Ottercast/OtterCastAmp/graphics/ottercast/enig.png

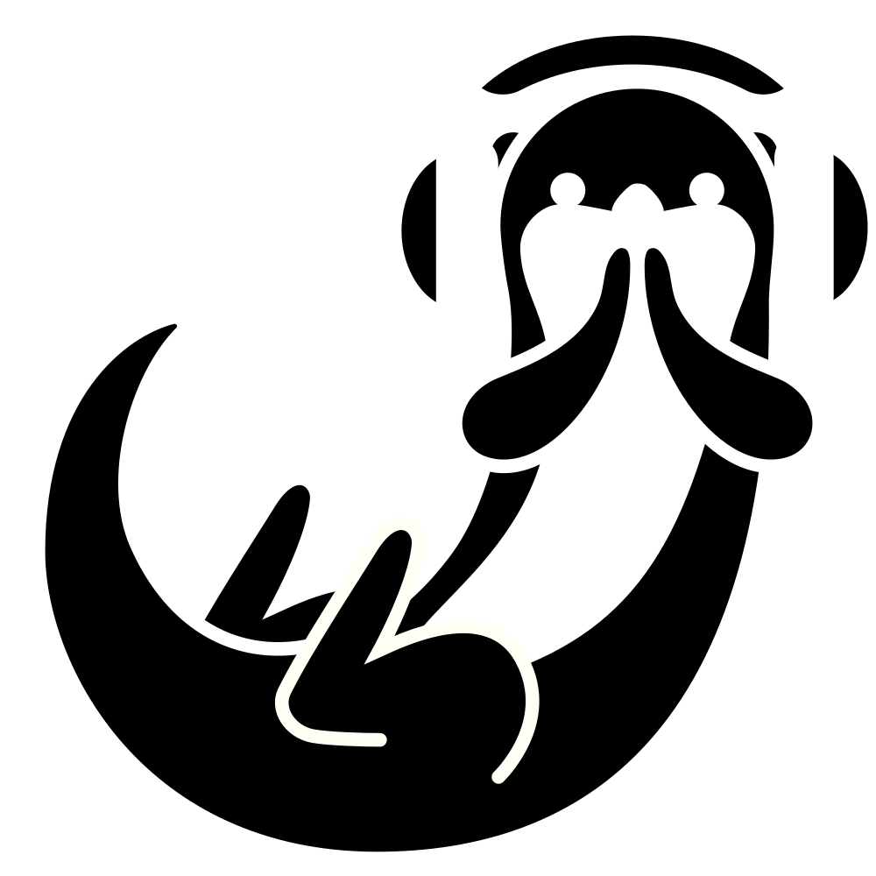
graphics/ottercast/enig.png
