Ottercast/OtterCastAmp/3D/u.Fl Antenna Connector - 523-A-1JB.STEP

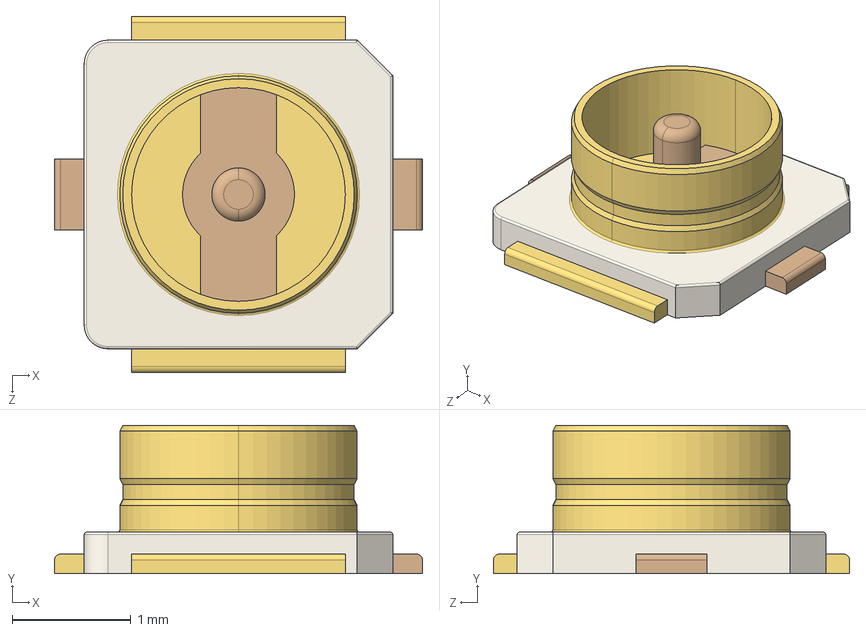
[picture p27: CAD file, 2021-03-01]
3D/u.Fl Antenna Connector - 523-A-1JB.STEP
3.10 x 1.25 x 3.00 mm
